atuleu/giant-snes-gamepad/firmware/src/Descriptor.c

#include "Descriptor.h"



const USB_Descriptor_HIDReport_Datatype_t  GamepadReport[] = { 
	HID_RI_USAGE_PAGE( 8 , 0x01 ),		// Generic Desktop
	HID_RI_USAGE(8 , 0x04),				// Joystick
	HID_RI_COLLECTION(8 , 0x01 ),		// Application collection
	    HID_RI_USAGE_PAGE(8, 0x09),		// Buttons 
	    HID_RI_USAGE_MINIMUM(8, 1),
	    HID_RI_USAGE_MAXIMUM(8, 12),
	    HID_RI_LOGICAL_MINIMUM(8 , 0),
	    HID_RI_LOGICAL_MAXIMUM(8 , 1),
	    HID_RI_REPORT_SIZE(8 , 1),
	    HID_RI_REPORT_COUNT(8 , 12),
	    HID_RI_INPUT(8 , HID_IOF_DATA | HID_IOF_VARIABLE | HID_IOF_ABSOLUTE), // says that the last are variable input
	    HID_RI_REPORT_SIZE(8 , 4),
	    HID_RI_REPORT_COUNT(8 , 1),
	    HID_RI_INPUT(8, HID_IOF_CONSTANT), //says 'forgets the 4 MSB bits !'
	HID_RI_END_COLLECTION(0),
};


const USB_Descriptor_Device_t DeviceDescriptor ={
	.Header						= {.Size = sizeof(USB_Descriptor_Device_t), .Type = DTYPE_Device},

	.USBSpecification			= VERSION_BCD(1,1,0),
	.Class						= USB_CSCP_NoDeviceClass,
	.SubClass					= USB_CSCP_NoDeviceSubclass,
	.Protocol					= USB_CSCP_NoDeviceProtocol,

	.Endpoint0Size				= FIXED_CONTROL_ENDPOINT_SIZE,

	.VendorID					= 0x03EB, // LUFA's VID
	.ProductID					= 0x2043, // LUFA Joystick
	.ReleaseNumber				= VERSION_BCD(0x69,0x04,0x02), //Unique version number to test if its ours device
	

	.ManufacturerStrIndex		= STR_MANUFACTURER,
	.ProductStrIndex			= STR_PRODUCT,
	.SerialNumStrIndex			= USE_INTERNAL_SERIAL,

	.NumberOfConfigurations		= FIXED_NUM_CONFIGURATIONS
};


const USB_Descriptor_String_t LanguageString = {
	.Header				= {.Size = USB_STRING_LEN(1), .Type = DTYPE_String},
	.UnicodeString		= {LANGUAGE_ID_ENG}
};

const USB_Descriptor_String_t ManufacturerString = {
	.Header				= {.Size = USB_STRING_LEN(9), .Type = DTYPE_String},
	.UnicodeString		= L"Satellite"
};

const USB_Descriptor_String_t ProductString	= {
	.Header				= {.Size = USB_STRING_LEN(18), .Type = DTYPE_String},
	.UnicodeString		= L"Giant SNES Gamepad"
};



const USB_Descriptor_Configuration_t ConfigurationDescriptor = {
	.Config = {
		.Header					= {.Size = sizeof(USB_Descriptor_Configuration_Header_t), .Type = DTYPE_Configuration },
		
		.TotalConfigurationSize = sizeof(USB_Descriptor_Configuration_t),
		.TotalInterfaces		= 1, //change here if other interfaces
		
		.ConfigurationNumber	= 1,
		.ConfigurationStrIndex	= NO_DESCRIPTOR,

		.ConfigAttributes		= (USB_CONFIG_ATTR_RESERVED | USB_CONFIG_ATTR_SELFPOWERED ),
		
		.MaxPowerConsumption	= USB_CONFIG_POWER_MA(100)
	},

	//add another one like size if more is needed
	.HID_Interface = {
		.Header					= {.Size = sizeof(USB_Descriptor_Interface_t), .Type = DTYPE_Interface},
		
		.InterfaceNumber		= IF_GAMEPAD,
		.AlternateSetting		= 0x00,

		.TotalEndpoints			= 1,


		.Class					= HID_CSCP_HIDClass,
		.SubClass				= HID_CSCP_NonBootSubclass,
		.Protocol				= HID_CSCP_NonBootProtocol,

		.InterfaceStrIndex		= NO_DESCRIPTOR
	},


	.HID_GamepadHID = {
		.Header					= {.Size = sizeof(USB_HID_Descriptor_HID_t), .Type = HID_DTYPE_HID },
		
		.HIDSpec				= VERSION_BCD(1,1,1),
		.CountryCode			= 0x00,
		.TotalReportDescriptors = 1,
		.HIDReportType			= HID_DTYPE_Report,
		.HIDReportLength		= sizeof(GamepadReport)
	},

	.HID_ReportINEndpoint = {
		.Header					= {.Size = sizeof(USB_Descriptor_Endpoint_t), .Type = DTYPE_Endpoint},
		
		.EndpointAddress		= GAMEPAD_IN_EPADDR,
		.Attributes				= (EP_TYPE_INTERRUPT | ENDPOINT_ATTR_NO_SYNC | ENDPOINT_USAGE_DATA),
		.EndpointSize			= GAMEPAD_IN_EPSIZE,
		.PollingIntervalMS		= 0x05 // \todo : reconsider increasing this

	},

};

#include "Gamepad.h"

uint16_t CALLBACK_USB_GetDescriptor(const uint16_t wValue,
                                    const uint8_t wIndex,
                                    const void** const descriptorAddress) {
	const uint8_t descriptorType = (wValue >> 8);
	const uint8_t descriptorNumber = (wValue & 0xff);
	
	const void * address = NULL;
	uint16_t size = NO_DESCRIPTOR;


	switch(descriptorType) {
	case DTYPE_Device :
		address = &DeviceDescriptor;
		size = sizeof(USB_Descriptor_Device_t);
		break;
	case DTYPE_Configuration:
		address = &ConfigurationDescriptor;
		size    = sizeof(USB_Descriptor_Configuration_t);
		break;
	case DTYPE_String:
		switch(descriptorNumber) {
		case STR_LANGUAGE:
			address = &LanguageString;
			size    = pgm_read_byte(&LanguageString.Header.Size);
			break;
		case STR_MANUFACTURER:
			address = &ManufacturerString;
			size    = pgm_read_byte(&ManufacturerString.Header.Size);
			break;
		case STR_PRODUCT:
			address = &ProductString;
			size    = pgm_read_byte(&ProductString.Header.Size);
			break;
		}
		break;
	case HID_DTYPE_HID:
		address = &ConfigurationDescriptor.HID_GamepadHID;
		size    = sizeof(USB_HID_Descriptor_HID_t);
		break;
	case HID_DTYPE_Report:
		address = &GamepadReport;
		size    = sizeof(GamepadReport);
		break;

	}
	*descriptorAddress = address;
	return size;
}
